Locoduino/CommandStation-EX-LaBox/Release_Notes/Railcom/La Box.jpg

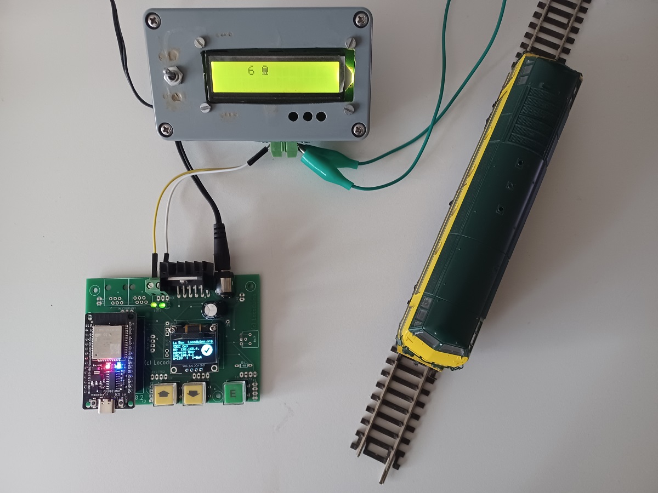
Release_Notes/Railcom/La Box.jpg
