Locoduino/CommandStation-EX-LaBox/Release_Notes/XpressNet/Double_RJ11E.jpg

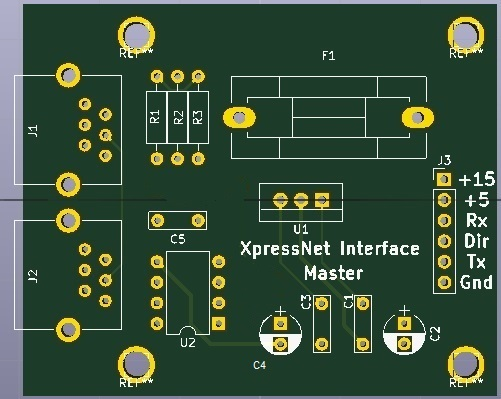
Release_Notes/XpressNet/Double_RJ11E.jpg
