Locoduino/CommandStation-EX-LaBox/Release_Notes/XpressNet/RJ11E.jpg

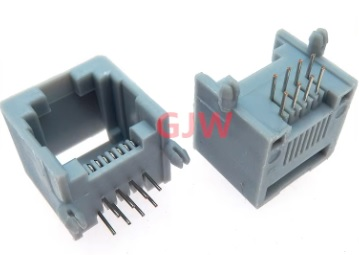
Release_Notes/XpressNet/RJ11E.jpg
