Locoduino/CommandStation-EX-LaBox/Release_Notes/XpressNet/Xpress1.jpg

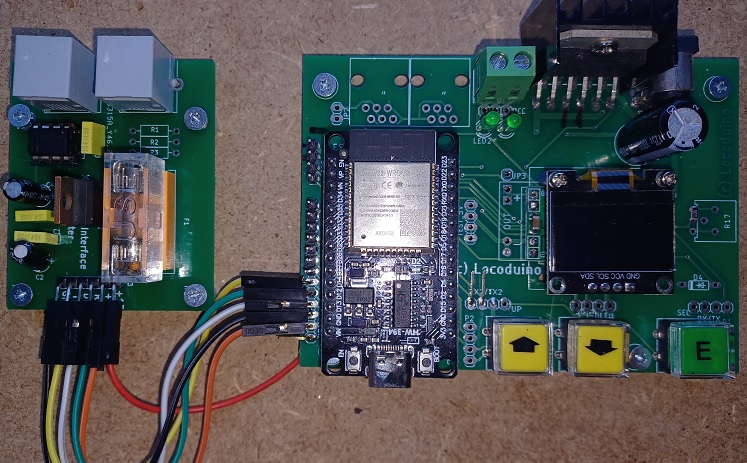
Release_Notes/XpressNet/Xpress1.jpg
