Locoduino/CommandStation-EX-LaBox/hmiConfig.h

/*
 * LaBox Project
 * Parameters
 * @Author : Cedric Bellec
 *	@Organization : Locoduino.org
 */

#ifndef HMICONFIG_H
#define HMICONFIG_H

// Pins
#define PIN_LEDBUILTIN           2
#define PIN_CURRENT_MES         36
#define PIN_VOLTAGE_MES         34

#ifdef USE_HMI
//---------------------- HMI section ------------------------------------
#define HMI_I2C_ADDR            0x3C
#define SCREEN_WIDTH            128         // OLED display width, in pixels
#define SCREEN_HEIGHT           64          // OLED display height, in pixels
#define HMI_Rotation            HMI_SCREEN_ROTATION           // 1 : 90°, 2 : 180°, 3 : 270°

// Pins
#define PIN_BTN_SEL             18
#define PIN_BTN_BTNUP           23
#define PIN_BTN_BTNDWN          19

// U/I correctors
#define HMI_VoltageK            0.0068      // Voltage scaling coefficient
#define HMI_CurrentK            0.9        	// Current scaling coefficient
#define HMI_deltaCurrent				HMI_CURRENTDELTA			// Current value shift with I=0
// Stack / string allocation sizes
#define HMI_StackNbCarElt       20          // 20 elements into the stack
#define HMI_EventMaxToDisplay   5           // We can display in full screnn 7 lines of event
#define HMI_MessageSize         20          // 20 characters for on message // Voir si il faut maintenir
#define HMI_MenueMessageSize    20          // 20 characters for un caption in menu
#define LineCarNbMax            20          // 1 ligne with FreeSerif9pt7b police, you can show 20 caracters max.
#define HMI_NbMemorisedTrain    10          // 
#define nbCycleToWaitWifi       50        
//--- Orders
#define HMI_OrderForward        20      
#define HMI_OrderBack           21
#define HMI_OrderStop           22 
#define HMI_OrderFunction       23
#define HMI_OrderStopAll        24  
#define HMI_StartDCC            25
#define HMI_ShortCurcuit        26
#define HMI_WifiWaiting         27
#define HMI_noWifi              28
#define HMI_WifiOk              29
//--- Display effects
#define HMI_LowEffect           500
#define HMI_FastEffect          100
#define HMI_DataRefesh          1000
#define HMI_DisplayRefesh       100
#define HMI_TimeOutMenu         30000     // in milliseconds
//--- HMITrain
#define HMITrain_NbMaxFunctions 28
#define HMITrain_NbStep         128
#define HMITrain_RectHeight     5
#define HMITrain_RectWidth      8
#define HMITrain_RectSpace      1
//--- Menu
#define HMI_Menu_OnLine         201
#define HMI_Menu_OffLine        202
#define HMI_Menu_WifiOn         203
#define HMI_Menu_WifiOff        204
#define NbMaxLineVisible        5

#define SPEED_VALUE_UNCHANGED		255

#define MENUNOTINIT             300
#define MENUEXIT                301
#define MENUCHANGETOCHILD       302
#define MENUCHOSEN              303
#define MENUTRAINADDRREAD       304
#define MENUTRAINCVREAD					305
#define MENUTRAINCVWRITE				306
#define MENUTRAINIDENT					307
#define MENUSHUTTLESAMPLE				308
#define MENUDCDCCMODE						309
#define MENUPHYSICALMES					310
#define MENUPROGMODE						311
#define MENUSETTINGS						312

#define MENUINFORMATION_ABOUT		400
#define MENUINFORMATION_WIFI		401
#define MENUINFORMATION_EXCOMM	402

#define MENUTYPECOMEBCK         0x8000
#define MENUTYPELIST            0x7999
#define MENUACTION              0x7998
#define MENUOPENSCREEN          0x7997
//#define MENUTYPEITEM            312


    // Message by language : French
// maximum line size : 					 ++++++++++++++++++++
#define TXT_Forward             "AV"
#define TXT_Back                "AR"
#define TXT_Forwardl            "Avance"
#define TXT_Backl               "Recule"
#define TXT_Stop                "Stop"
#define TXT_Function            "F"
#define TXT_StopAll             "<ARRET DCC>"
#define TXT_StartDCC            "<DCC On>"
#define TXT_ShortCircuit        "COURT-CIRCUIT"
#define TXT_MenuDCCOffLine      "Power ON/OFF"
#define TXT_MenuOnLine          "En ligne"
#define TXT_MenuOffLine         "Hors ligne"
#define TXT_MenuResetConfirm    "Confirmation Reset"
#define TXT_MenuYes             "Oui"
#define TXT_MenuNo              "Non"
#define TXT_MenuParams          "Parametres"
#define TXT_MenuInfos						"Informations"
#define TXT_MenuAbout						"A propos de..."
#define TXT_MenuAboutCSEX				"CS-EX %s <sortie>"
#define TXT_MenuInfoButtons			"             <sortie>"
#define TXT_MenuProgButtons			" ^ v         <sortie>"
#define TXT_MenuWifiInfo        "WiFi"
#define TXT_MenuEXCOMMInfo			"EXCOMM"
#define TXT_MenuSoftReset       "Redemarrage"
#define TXT_MenuBack            "< Retour >"
#define TXT_MenuAddrRead        "Lecture adr Train"
#define TXT_MenuAddrRetry				"Relire"
#define TXT_MenuAddrQuit				"Quitter"
#define TXT_MenuCVRead        	"Lecture CV"
#define TXT_MenuCVWrite        	"Ecriture CV"
#define TXT_MenuIdent	        	"Ident. decodeur"
#define TXT_MenuShuttle	       	"Va&Vient EXRail"
#define TXT_MenuSettings       	"Reglages"
#define TXT_DcDccMode		       	"DC/DCC"
#define TXT_PhysicalMes         "Mesures U et I"
#define TXT_ProgMode		        "Mode Programmation"
#define TXT_TrainView           "Type de vue trains"
#define TXT_V1Train             "1 train"
#define TXT_V2Trains            "2 trains"
#define TXT_V3Trains            "3 trains"
#define TXT_DONOTRESTART				"Redémarrer LaBox !"
#define TXT_ON									"ON"
#define TXT_OFF									"OFF"
#define TXT_CHANGE							"Changer"
// maximum line size : 					 ++++++++++++++++++++
#define TXT_LstEvent            "Liste evenements"
#define TXT_WifiWaiting         "Connexion WiFi..."
#define TXT_noWifi              " !! Pas de WiFi !!"
#define TXT_WifiApOk            "...Wifi AP ok..."
#define TXT_WifiSTAOk           "...Wifi STA ok..."
#define TXT_BoxAddr             "Adresse Box:"
#define TXT_WIFI								"WiFi"
#define TXT_RAILCOM							"Railcom"
// maximum line size : 					 ++++++++++++++++++++
#define TXT_CVREAD_LOGO					"LaBox     CV Lecture"
#define TXT_CVWRITE_LOGO				"LaBox    CV Ecriture"
#define TXT_CVRW_CVVALUE				"CV      Valeur"
#define TXT_CVRW_CVOK						"CV      Valeur OK"
#define TXT_CVRW_CVFAIL					"CV    Valeur ECHEC"
#define TXT_CVREAD_READING			"       Lecture..."
#define TXT_CVWRITE_WRITING			"      Ecriture..."
#define TXT_CVRW_OK							"AutreCV      Quitter"
#define TXT_CVRW_FAIL						"Refaire +/-  Quitter"
#define TXT_CVRW_READY					"+            Quitter"
#define TXT_CVREAD_ADDRESS			"+ -             Lire"
#define TXT_CVWRITE_ADDRESS			"+ -           Valeur"
#define TXT_CVWRITE_VALUE				"+ -           Ecrire"
// maximum line size : 					 ++++++++++++++++++++
#define TXT_IDENT_LOGO					"LaBox       Decodeur"
#define TXT_IDENT_READING7			"         Lecture cv7"
#define TXT_IDENT_READING8			"         Lecture cv8"
#define TXT_IDENT_LOCOADDRESS		"+ -           Lancer"
#define TXT_IDENT_ERRORCV7			"ERREUR CV7"
#define TXT_IDENT_ERRORCV8			"ERREUR CV8 cv7=%d"
#define TXT_IDENT_UNKNOWNID			"Inconnu cv8=%d"
#define TXT_IDENT_SEENMRA				"See NMRA 9.2.2.5 pdf"
#define TXT_IDENT_VERSION				"Version: %d/%d"
// maximum line size : 					 ++++++++++++++++++++
#define TXT_SHUTTLE_LOGO				"LaBox EXRail shuttle"
#define TXT_SHUTTLE_RUNNING			"Va&Vient EN ROUTE"
#define TXT_SHUTTLE_STOP				"Stop"
// maximum line size : 					 ++++++++++++++++++++
#define TXT_DCDCC_LOGO					"LaBox   DC/DCC mode"
#define TXT_DCDCC_DCRUNNING			"DC"
#define TXT_DCDCC_DCCRUNNING		"DCC"

    // Message by language : English
// maximum line size : 					 ++++++++++++++++++++
/*#define TXT_Forward             "FW"
#define TXT_Back                "BK"
#define TXT_Forwardl            "Forward"
#define TXT_Backl               "Back"
#define TXT_Stop                "Stop"
#define TXT_Function            "F"
#define TXT_StopAll             "!STOP ALL!"
#define TXT_StartDCC            "<DCC On>"
#define TXT_ShortCircuit        "SHORT-CIRCUIT"
#define TXT_MenuDCCOffLine      "Power ON/OFF"
#define TXT_MenuOnLine          "On line"
#define TXT_MenuOffLine         "Off line"
#define TXT_MenuDHCP            "DHCP"
#define TXT_MenuResetConfirm    "Reset confirmation ?"
#define TXT_MenuYes             "Yes"
#define TXT_MenuNo              "No"
#define TXT_MenuParams          "Parameters"
#define TXT_MenuInfos						"Informations"
#define TXT_MenuAbout						"About..."
#define TXT_MenuAboutCSEX				"CS-EX %s   <quit>"
#define TXT_MenuInfoButtons			"               <quit>"
#define TXT_MenuProgButtons			" ^ v           <quit>"
#define TXT_MenuWifiInfo        "WiFi"
#define TXT_MenuEXCOMMInfo			"EXCOMM"
#define TXT_MenuCAN             "Networks CAN"
#define TXT_MenuSoftReset       "Reboot"
#define TXT_MenuBack            "< Return >"
#define TXT_MenuAddrRead        "Read Train Addr"
#define TXT_MenuAddrRetry				"Retry"
#define TXT_MenuAddrQuit				"Quit"
#define TXT_MenuCVRead        	"Read CV"
#define TXT_MenuCVWrite        	"Write CV"
#define TXT_MenuIdent	        	"Identify decoder"
#define TXT_MenuShuttle	       	"Shuttle EXRail"
#define TXT_MenuSettings       	"Settings"
#define TXT_PhysicalMes         "Measures U and I"
#define TXT_ProgMode		        "Programming Mode"
#define TXT_TrainView           "Train view"
#define TXT_V1Train             "1 train"
#define TXT_V2Trains            "2 trains"
#define TXT_V3Trains            "3 trains"
#define TXT_DONOTRESTART				"Restart LaBox !"
#define TXT_ON									"ON"
#define TXT_OFF									"OFF"
#define TXT_CHANGE							"Change"
// maximum line size : 					 ++++++++++++++++++++
#define TXT_LstEvent            "Event list"
#define TXT_WifiWaiting         "Connection WiFi..."
#define TXT_noWifi              " !! No WiFi !!"
#define TXT_WifiApOk            "...Wifi AP ok..."
#define TXT_WifiSTAOk           "...Wifi STA ok..."
#define TXT_BoxAddr             "Box address :"
#define TXT_WIFI								"WiFi"
#define TXT_RAILCOM							"Railcom"
// maximum line size : 					 ++++++++++++++++++++
#define TXT_CVREAD_LOGO					"LaBox        CV Read"
#define TXT_CVWRITE_LOGO				"LaBox       CV Write"
#define TXT_CVRW_CVVALUE				"CV      Value"
#define TXT_CVRW_CVOK						"CV      Value OK"
#define TXT_CVRW_CVFAIL					"CV      Value FAIL"
#define TXT_CVREAD_READING			"       Reading..."
#define TXT_CVWRITE_WRITING			"       Writing..."
#define TXT_CVRW_OK							"OtherCV         Quit"
#define TXT_CVRW_FAIL						"Redo +/-        Quit"
#define TXT_CVRW_READY					"+               Quit"
#define TXT_CVREAD_ADDRESS			"+ -             Read"
#define TXT_CVWRITE_ADDRESS			"+ -            Value"
#define TXT_CVWRITE_VALUE				"+ -            Write"
// maximum line size : 					 ++++++++++++++++++++
#define TXT_IDENT_LOGO					"LaBox        Decoder"
#define TXT_IDENT_READING7			"         Reading cv7"
#define TXT_IDENT_READING8			"         Reading cv8"
#define TXT_IDENT_LOCOADDRESS		"+ -            Start"
#define TXT_IDENT_ERRORCV7			"ERROR CV7"
#define TXT_IDENT_ERRORCV8			"ERROR CV8 cv7=%d"
#define TXT_IDENT_UNKNOWNID			"Unknown cv8=%d"
#define TXT_IDENT_SEENMRA				"See NMRA 9.2.2.5 pdf"
#define TXT_IDENT_VERSION				"Version: %d/%d"
// maximum line size : 					 ++++++++++++++++++++
#define TXT_SHUTTLE_LOGO				"LaBox EXRail shuttle"
#define TXT_SHUTTLE_RUNNING			"Shuttle RUNNING"
#define TXT_SHUTTLE_STOP				"Stop"
// maximum line size : 					 ++++++++++++++++++++
#define TXT_DCDCC_LOGO					"LaBox   DC/DCC mode"
#define TXT_DCDCC_DCRUNNING			"DC"
#define TXT_DCDCC_DCCRUNNING		"DCC"
*/

//---------------------- Global section ---------------------------------
#define Labox_StateDCCOFF        101
#define Labox_StateDCCON         102
#define Labox_StateSHORTCIRCUIT  103

#endif
#endif
