Locoduino/CommandStation-EX-LaBox/Z21Throttle.cpp

/*
 *  © 2023 Thierry Paris / Locoduino
 *  © 2023,2024 Harald Barth
 *  All rights reserved.
 *  
 *  This file is part of CommandStation-EX-Labox
 *
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
 *  You should have received a copy of the GNU General Public License
 *  along with CommandStation.  If not, see <https://www.gnu.org/licenses/>.
 */
#include <Arduino.h>
#include "defines.h"

#ifdef ENABLE_Z21

#include "Z21Throttle.h"
#include "DCC.h"
#include "WifiESP32.h"
#include "DCCWaveform.h"
#include "StringFormatter.h"
#include "Turnouts.h"
#include "Sensors.h"
#include "DIAG.h"
#include "GITHUB_SHA.h"
#include "version.h"
#include "EXRAIL2.h"
#include "TrackManager.h"
#include "DCCTimer.h"
#include "LaboxModes.h"
#ifdef USE_HMI
	#include "hmi.h"
#endif

static std::vector<NetworkClientUDP> clientsUDP; // a list to hold all UDP clients

bool Z21Throttle::DIAGBASE=false;
bool Z21Throttle::DIAGRWCV=false;
bool Z21Throttle::DIAGBROADCAST=false;
bool Z21Throttle::DIAGDATA=false;
bool Z21Throttle::DIAGVERBOSE=false;

#define DIAG_Z21	 				if (Z21Throttle::DIAGBASE) DIAG
#define DIAG_Z21RWCV			if (Z21Throttle::DIAGRWCV) DIAG
#define DIAG_Z21BROADCAST	if (Z21Throttle::DIAGBROADCAST) DIAG
#define DIAG_Z21DATA		 	if (Z21Throttle::DIAGDATA) DIAG
#define DIAG_Z21VERBOSE	 	if (Z21Throttle::DIAGVERBOSE) DIAG

#define LOOPLOCOS(CAB)  for (int loco=0;loco<MAX_MY_LOCO;loco++)
#define LOOPTHROTTLES  Z21Throttle *pLoopThrottle = Z21Throttle::getFirstThrottle(); for (; pLoopThrottle != NULL; pLoopThrottle = pLoopThrottle->getNextThrottle())
#define LOOPCLIENTS  for (int clientId = 0; clientId < clientsUDP.size(); clientId++)

#define TURNOUT_FAR_TO_ADDRESS(inMSB, inLSB) ((inMSB << 8) + inLSB + 1)
#define TURNOUT_ADDRESS_TO_FARMSB(addr) ((byte)((addr-1) >> 8))
#define TURNOUT_ADDRESS_TO_FARLSB(addr) ((byte)((addr-1) & 0xFF))

Z21Throttle *Z21Throttle::firstThrottle=NULL;
byte Z21Throttle::commBuffer[100];
byte Z21Throttle::replyBuffer[20];

Z21Throttle* Z21Throttle::readWriteThrottle = NULL;
int Z21Throttle::cvAddress = -1;
int Z21Throttle::cvValue = -1;
int Z21EXCommItem::UDPport = Z21_UDPPORT;

void printClientsUDP();

WiFiUDP NetworkClientUDP::client;

bool Z21EXCommItem::begin() {
#ifdef DCCPP_DEBUG_MODE
	CircularBuffer::Test();
#endif
	bool retf = true;

	IPAddress ip;

	if (WiFi.getMode() == wifi_mode_t::WIFI_MODE_STA)
		ip = WiFi.localIP();
	if (WiFi.getMode() == wifi_mode_t::WIFI_MODE_AP)
		ip = WiFi.softAPIP();	

	uint8_t ret = NetworkClientUDP::client.begin(ip, UDPport);
	if (ret == 1) {
		retf = true;
		NetworkClientUDP::client.flush();
	}

	if (retf)
    DIAG(F("[Z21] UDP Connection started port %d. Z21 apps are available."), UDPport);
  else {
		DIAG(F("[Z21] UDP Connection failed. Z21 apps not available."));
		UDPport = -1;
	}

	return retf;
}

void Z21EXCommItem::getInfos(String *pMess1, String *pMess2, String *pMess3, byte maxSize) 
{
	char mess[maxSize*2];

	if (UDPport == -1)
		sprintf(mess, "[Z21] Not connected");
	else
		sprintf(mess, "[Z21] Port %d", UDPport);

	*pMess1 = mess;
}

void Z21EXCommItem::broadcastLoco(int16_t cab) {
	if (Z21Throttle::getFirstThrottle()!=NULL)		DIAG_Z21BROADCAST(F("[Z21] start Broadcasting loco %d ----"), cab);
	LOOPTHROTTLES {
		DIAG_Z21BROADCAST(F("[Z21] check throttle %d for loco %d %d %s"), pLoopThrottle->getClientId(), cab, pLoopThrottle->isBroadcastFlag() ? "BROADCAST" : "no broadcast");
		if (pLoopThrottle->isBroadcastFlag()) {
			int DB2 = cab & 0xFF;          // Extraction de inDB2
			int DB1 = (cab >> 8) & 0x3F;   // Extraction de inDB1
			pLoopThrottle->notifyLocoInfo(DB1, DB2);
		}
	}
	if (Z21Throttle::getFirstThrottle()!=NULL)		DIAG_Z21BROADCAST(F("[Z21] end Broadcasting locos   ----"));
}

void Z21EXCommItem::broadcastSensor(int16_t id, bool value) {
if (Z21Throttle::getFirstThrottle()!=NULL)			DIAG_Z21BROADCAST(F("[Z21] start Broadcasting sensors ----"));
	LOOPTHROTTLES {
		if (pLoopThrottle->isBroadcastFlag()) { // Should be broadcasted only with BROADCAST_LOCONET_DETECTOR flag...
			pLoopThrottle->notifySensor(id);
		}
	}
	if (Z21Throttle::getFirstThrottle()!=NULL)		DIAG_Z21BROADCAST(F("[Z21] end Broadcasting sensors   ----"));
}

void Z21EXCommItem::broadcastTurnout(int16_t id, bool isClosed) {
	if (Z21Throttle::getFirstThrottle()!=NULL)		DIAG_Z21BROADCAST(F("[Z21] start Broadcasting turnouts ----"));
	LOOPTHROTTLES {
		if (pLoopThrottle->isBroadcastFlag()) {
			int DB1 = TURNOUT_ADDRESS_TO_FARMSB(id);
			int DB2 = TURNOUT_ADDRESS_TO_FARLSB(id);
			pLoopThrottle->notifyTurnoutInfo((byte)DB1, (byte)DB2);
		}
	}
	if (Z21Throttle::getFirstThrottle()!=NULL)		DIAG_Z21BROADCAST(F("[Z21] end Broadcasting turnouts   ----"));
}

void Z21EXCommItem::broadcastPower() {
	if (Z21Throttle::getFirstThrottle()!=NULL)		DIAG_Z21BROADCAST(F("[Z21] start Broadcasting power ----"));
	LOOPTHROTTLES {
			pLoopThrottle->notifyTrPw(TrackManager::getMainPower() == POWERMODE::ON ? 1 : 0);
	}
	if (Z21Throttle::getFirstThrottle()!=NULL)		DIAG_Z21BROADCAST(F("[Z21] end Broadcasting power   ----"));
}

int readUdpPacket() {
	byte udp[UDPBYTE_SIZE];
	memset(udp, 0, UDPBYTE_SIZE);
	int len = NetworkClientUDP::client.read(udp, UDPBYTE_SIZE);
	if (len > 0) {
		for (int clientId = 0; clientId < clientsUDP.size(); clientId++) {
			if (clientsUDP[clientId].inUse) {
				if (clientsUDP[clientId].remoteIP == NetworkClientUDP::client.remoteIP() && clientsUDP[clientId].remotePort == NetworkClientUDP::client.remotePort()) {
					DIAG_Z21DATA(F("[Z21] %d: <- udp_len:%d"), clientId, len);

					// Black Z21 Android app send a bunch of 1000 bytes of value 0 ! 
					// Dont know why, but do not add this to the circular buffer !
					if (len < Z21_MAXIMAL_UDP_MSG_SIZE) {
						clientsUDP[clientId].pudpBuffer->PushBytes(udp, len);

						//if (Z21Throttle::Z21THROTTLEDATA) clientsUDP[clientId].pudpBuffer->printStatus();
					}
					else {
						DIAG_Z21(F("[Z21] %d: <- long message ignored : udp_len:%d   first byte : %d"), clientId, len, udp[0]);

						if (Z21Throttle::DIAGDATA) {
							for(int i = 0; i < 10; i++) {
								if (len > i*10) {
									DIAG_Z21DATA(F("   UDP %d-%d : 0x%02x 0x%02x 0x%02x 0x%02x 0x%02x 0x%02x 0x%02x 0x%02x 0x%02x 0x%02x"),
															i*10, (i*10)+9,
															(len > i*10)      ?udp[i*10]:0,
															(len > (i*10) + 1)?udp[(i*10)+1]:0,
															(len > (i*10) + 2)?udp[(i*10)+2]:0,
															(len > (i*10) + 3)?udp[(i*10)+3]:0,
															(len > (i*10) + 4)?udp[(i*10)+4]:0,
															(len > (i*10) + 5)?udp[(i*10)+5]:0,
															(len > (i*10) + 6)?udp[(i*10)+6]:0,
															(len > (i*10) + 7)?udp[(i*10)+7]:0,
															(len > (i*10) + 8)?udp[(i*10)+8]:0,
															(len > (i*10) + 9)?udp[(i*10)+9]:0);
								}
							}
						}
					}

					return clientId;
				}
			}
		}
	}

	return -1;
}

void Z21Throttle::loop() {
  if (Z21EXCommItem::UDPport < 0) {
		return;
	}

	int clientId = 0;

	// loop over all clients and remove inactive
	for (clientId = 0; clientId < clientsUDP.size(); clientId++) {
		if (!clientsUDP[clientId].inUse) {
			continue;
		}

		Z21Throttle* pThrottle = getOrAddThrottle(clientId); 

		if (pThrottle->lastHeartBeatDate != 0 && millis() - pThrottle->lastHeartBeatDate > Z21_TIMEOUT) {
			clientsUDP[clientId].connected = false;
		}

		// check if client is there and alive
		if (clientsUDP[clientId].inUse && !clientsUDP[clientId].connected) {
			DIAG(F("[Z21] Remove disconnected UDP client %d"), clientId);
			clientsUDP[clientId].inUse = false;
			printClientsUDP();
		}
	}

	int len = NetworkClientUDP::client.parsePacket();
	if (len > 0) {
		// Check if this IP is already in the client list.
		int clientId = 0;
		for (; clientId < clientsUDP.size(); clientId++) {
			if (clientsUDP[clientId].inUse) {
				if (clientsUDP[clientId].remoteIP == NetworkClientUDP::client.remoteIP() && clientsUDP[clientId].remotePort == NetworkClientUDP::client.remotePort()) {
					//DIAG_Z21VERBOSE(F("UDP client %d : %s Already connected"), clientId, clientsUDP[clientId].remoteIP.toString().c_str());
					break;
				}
			}
		}

		// If this IP is not already present, try tyo find the first slot available

		if (clientId >= clientsUDP.size()) {
			for (clientId = 0; clientId < clientsUDP.size(); clientId++) {
				if (!clientsUDP[clientId].inUse) {
					break;
				}
			}

			// If no empty slot found, add a new one.
			if (clientId >= clientsUDP.size()) {
				NetworkClientUDP nc;
				clientsUDP.push_back(nc);
			}

			clientsUDP[clientId].remoteIP = NetworkClientUDP::client.remoteIP();
			clientsUDP[clientId].remotePort = NetworkClientUDP::client.remotePort();
			clientsUDP[clientId].connected = true;
			clientsUDP[clientId].inUse = true;

			DIAG(F("[Z21] New UDP client %d, %s"), clientId, clientsUDP[clientId].remoteIP.toString().c_str());
			printClientsUDP();
			#ifdef USE_HMI
			if (hmi::CurrentInterface != NULL) hmi::CurrentInterface->NewClient(clientId, clientsUDP[clientId].remoteIP, 0);
			#endif
			// Fleischmann/Roco Android app starts with Power on !
			TrackManager::setMainPower(POWERMODE::ON);
			Z21Throttle* pThrottle = getOrAddThrottle(clientId); 
			if (pThrottle != NULL) {
		  	pThrottle->lastHeartBeatDate = millis();
//      	pThrottle->notifyTrPw(clientId, 1);
			}
		}

		clientId = readUdpPacket();

		if (clientId >= 0) {
			if (clientsUDP[clientId].ok()) {        
				Z21Throttle* pThrottle = getOrAddThrottle(clientId); 
			  pThrottle->lastHeartBeatDate = millis();

				if (pThrottle != NULL) {
					while(clientsUDP[clientId].pudpBuffer->GetCount() > 2)
						pThrottle->parse();
				}
			}
		}
	}
}

/** Print the list of assigned locomotives. */
void Z21Throttle::printLocomotives(bool addTab) {
	if (!Z21Throttle::DIAGBASE)
		return;

	DIAG(F("[Z21]       Locomotives ------------------"));
	for (int loco = 0; loco < MAX_MY_LOCO; loco++)
		if (this->cabs[loco] != 0)
			DIAG(F("[Z21] %s         %d : cab %d on throttle %c"), addTab ? "   ":"", loco, this->cabs[loco], this->clientid);
}

/** Print the list of UDP clients. */
void printClientsUDP() {
	if (!Z21Throttle::DIAGBASE) return;

	DIAG(F("[Z21]       UDP Clients ------------------"));
	for (int clientId = 0; clientId < clientsUDP.size(); clientId++)
		if (clientsUDP[clientId].ok())
			DIAG(F("[Z21]          %d %s: %s:%d"), clientId, clientsUDP[clientId].connected?"Connected":"Not connected", clientsUDP[clientId].remoteIP.toString().c_str(), clientsUDP[clientId].remotePort);
		else
			DIAG(F("[Z21]          %d unused"), clientId);
}

/** Print the list of throttles. */
void Z21Throttle::printThrottles(bool inPrintLocomotives) {
	if (!Z21Throttle::DIAGBASE)	return;

	DIAG(F("[Z21]       Throttles ---------------"));
	for (Z21Throttle* wt = firstThrottle; wt != NULL; wt = wt->nextThrottle) {
		if (wt->clientid == -1)
			DIAG(F("[Z21]          unused"));
		else {
			DIAG(F("[Z21]          %d : %d.%d.%d.%d:%d"), wt->clientid, 
			clientsUDP[wt->clientid].remoteIP[0], 
			clientsUDP[wt->clientid].remoteIP[1], 
			clientsUDP[wt->clientid].remoteIP[2], 
			clientsUDP[wt->clientid].remoteIP[3], 
			clientsUDP[wt->clientid].remotePort);

			if (inPrintLocomotives)
				wt->printLocomotives(true);
		}
	}
}

Z21Throttle* Z21Throttle::getOrAddThrottle(int clientId) {
	for (Z21Throttle* wt = firstThrottle; wt != NULL ; wt = wt->nextThrottle)  {
		if (wt->clientid == clientId)
			return wt; 
	}

	Z21Throttle *p = new Z21Throttle(clientId);
	printThrottles(false);
	return p;
}

/*void Z21Throttle::broadcastNotifyTurnout(uint16_t addr, bool isClosed) {
  for (Z21Throttle* wt = firstThrottle; wt != NULL ; wt = wt->nextThrottle)  {
    wt->notifyTurnoutInfo(addr, isClosed);
  }
}
void Z21Throttle::broadcastNotifySensor(uint16_t addr, bool state) {
  for (Z21Throttle* wt = firstThrottle; wt != NULL ; wt = wt->nextThrottle)  {
    wt->notifySensor(addr, state);
  }
}*/

void Z21Throttle::forget( byte clientId) {
	for (Z21Throttle* wt=firstThrottle; wt!=NULL ; wt=wt->nextThrottle)  
    	if (wt->clientid==clientId) {
			delete wt;
			break; 
		}
}

bool Z21Throttle::isThrottleInUse(int cab) {
	for (Z21Throttle* wt=firstThrottle; wt!=NULL ; wt=wt->nextThrottle)  
		if (wt->isCabInUse(cab)) return true;

	return false;
}

// One instance of Z21Throttle per connected client, so we know what the locos are 
 
Z21Throttle::Z21Throttle(int inClientId) {
	this->clientid = inClientId;
	DIAG_Z21(F("[Z21] new Throttle for client UDP %d"),this->clientid);
	this->nextThrottle = firstThrottle;
	this->firstThrottle = this;
	this->turnoutListHash = -1;  // make sure turnout list is sent once
	this->exRailSent = false;
	this->lastHeartBeatDate = 0;
	// Because if the LaBox restarts but not the Z21 app, the Z21 app will not resend the LAN_SET_BROADCASTFLAGS, we need to set the default value of broadcast flags to be able to broadcast loco and turnout infos to the app.
	this->broadcastFlags = BROADCAST_BASE; // by default, basic broadcast flag is on
	for (int loco=0;loco<MAX_MY_LOCO; loco++)
		this->cabs[loco]=0;
}

Z21Throttle::~Z21Throttle() {
	DIAG_Z21(F("[Z21] Deleting Throttle client UDP %d"),this->clientid);
	if (firstThrottle== this) {
		firstThrottle=this->nextThrottle;
		return;
	}

	for (Z21Throttle* wt=firstThrottle; wt!=NULL ; wt=wt->nextThrottle) {
		if (wt->nextThrottle==this) {
			wt->nextThrottle=this->nextThrottle;
			return;  
		}
	}
}

void Z21Throttle::write(byte* inpData, int inLengthData) {
	size_t size = 0;

//	if (this->dontReply)
//		return;
	
	int errorCode = NetworkClientUDP::client.beginPacket(clientsUDP[this->clientid].remoteIP, clientsUDP[this->clientid].remotePort);
	if (errorCode != 1) {
		DIAG_Z21(F("[Z21] %d: UDP beginPacket failed with error code %d"), this->clientid, errorCode);
		return;
	}
	size = NetworkClientUDP::client.write(inpData, inLengthData);
	errorCode = NetworkClientUDP::client.endPacket();
	if (errorCode != 1) {
		DIAG_Z21(F("[Z21] %d: UDP endPacket failed with error code %d"), this->clientid, errorCode);
		return;
	}
	
	DIAG_Z21DATA(F("[Z21] %d: %s SENT 0x%02x 0x%02x 0x%02x 0x%02x 0x%02x 0x%02x 0x%02x 0x%02x 0x%02x 0x%02x"), this->clientid,
                          size == 0 ? "BINARY NOT" :"",
                          (inLengthData > 0)?inpData[0]:0,
                          (inLengthData > 1)?inpData[1]:0,
                          (inLengthData > 2)?inpData[2]:0,
                          (inLengthData > 3)?inpData[3]:0,
                          (inLengthData > 4)?inpData[4]:0,
                          (inLengthData > 5)?inpData[5]:0,
                          (inLengthData > 6)?inpData[6]:0,
                          (inLengthData > 7)?inpData[7]:0,
                          (inLengthData > 8)?inpData[8]:0,
                          (inLengthData > 9)?inpData[9]:0);
}

// sizes : [       2        ][       2        ][inLengthData]
// bytes : [length1, length2][Header1, Header2][Data........]
bool Z21Throttle::notify(unsigned int inHeader, byte* inpData, unsigned int inLengthData, bool inXorInData) {
	int realLength = (inLengthData + 4 + (inXorInData == false ? 1 : 0));

	Z21Throttle::commBuffer[0] = realLength % 256;
	Z21Throttle::commBuffer[1] = realLength / 256;
	Z21Throttle::commBuffer[2] = inHeader % 256;
	Z21Throttle::commBuffer[3] = inHeader / 256;
	memcpy(Z21Throttle::commBuffer + 4, inpData, inLengthData);

	if (!inXorInData) {    // if xor byte not included in data, compute and write it !
		byte xxor = 0;

		for (unsigned int i = 0; i < inLengthData; i++)
			xxor ^= inpData[i];

		Z21Throttle::commBuffer[inLengthData+4] = xxor;
	}

	write(Z21Throttle::commBuffer, realLength);

	return true;
}

// sizes : [       2        ][       2        ][   1   ][inLengthData]
// bytes : [length1, length2][Header1, Header2][XHeader][Data........]
bool Z21Throttle::notify(unsigned int inHeader, unsigned int inXHeader, byte* inpData, unsigned int inLengthData, bool inXorInData) {
	int realLength = (inLengthData + 5 + (inXorInData == false ? 1 : 0));

	Z21Throttle::commBuffer[0] = realLength % 256;
	Z21Throttle::commBuffer[1] = realLength / 256;
	Z21Throttle::commBuffer[2] = inHeader % 256;
	Z21Throttle::commBuffer[3] = inHeader / 256;
	Z21Throttle::commBuffer[4] = inXHeader;
	memcpy(Z21Throttle::commBuffer + 5, inpData, inLengthData);

	if (!inXorInData) {    // if xor byte not included in data, compute and write it !
		byte xxor = inXHeader;

		for (unsigned int i = 0; i < inLengthData; i++)
			xxor ^= inpData[i];

		Z21Throttle::commBuffer[inLengthData + 5] = xxor;
	}

	write(Z21Throttle::commBuffer, realLength);

	return true;
}

// sizes : [       2        ][       2        ][   1   ][ 1 ][inLengthData]
// bytes : [length1, length2][Header1, Header2][XHeader][DB0][Data........]
bool Z21Throttle::notify(unsigned int inHeader, unsigned int inXHeader, byte inDB0, byte* inpData, unsigned int inLengthData, bool inXorInData) {
	int realLength = (inLengthData + 6 + (inXorInData == false ? 1 : 0));

	Z21Throttle::commBuffer[0] = realLength % 256;
	Z21Throttle::commBuffer[1] = realLength / 256;
	Z21Throttle::commBuffer[2] = inHeader % 256;
	Z21Throttle::commBuffer[3] = inHeader / 256;
	Z21Throttle::commBuffer[4] = inXHeader;
	Z21Throttle::commBuffer[5] = inDB0;
	memcpy(Z21Throttle::commBuffer + 6, inpData, inLengthData);

	if (!inXorInData) {   // if xor byte not included in data, compute and write it !
		byte xxor = inXHeader^inDB0;

		for (unsigned int i = 0; i < inLengthData; i++)
			xxor ^= inpData[i];

		Z21Throttle::commBuffer[inLengthData + 6] = xxor;
	}

	write(Z21Throttle::commBuffer, realLength);

	return true;
}

void Z21Throttle::notifyStatus() {
	Z21Throttle::replyBuffer[0] = 0; // main current 1
	Z21Throttle::replyBuffer[1] = 0; // main current 2
	Z21Throttle::replyBuffer[2] = 0; // prog current 1
	Z21Throttle::replyBuffer[3] = 0; // prog current 2
	Z21Throttle::replyBuffer[4] = 0; // filtered main current 1
	Z21Throttle::replyBuffer[5] = 0; // filtered main current 2
	Z21Throttle::replyBuffer[6] = 0; // Temperature 1
	Z21Throttle::replyBuffer[7] = 0; // Temperature 2
	Z21Throttle::replyBuffer[8] = 5; // Supply voltage 1
	Z21Throttle::replyBuffer[9] = 0; // supply voltage 2
	Z21Throttle::replyBuffer[10] = 16; // VCC voltage 1 
	Z21Throttle::replyBuffer[11] = 0; // VCC voltage 2
	Z21Throttle::replyBuffer[12] = 0b00000000;	// CentralState 
	Z21Throttle::replyBuffer[13] = 0b00000000; // CentralStateEx
	Z21Throttle::replyBuffer[14] = 0;
	Z21Throttle::replyBuffer[15] = 0;
	notify(HEADER_LAN_SYSTEMSTATE, Z21Throttle::replyBuffer, 16, true);
}

int Z21Throttle::getOrAddLoco(int cab) {
	int loco = 0;

	// try to find the cab
	for (; loco < MAX_MY_LOCO; loco++) {
		if (this->cabs[loco] == cab) 
			return loco;
	}

	int foundLoco = -1;

	// not found ! Add the cab.
	for (loco = 0; loco < MAX_MY_LOCO; loco++) {
		if (this->cabs[loco] == 0) {
			this->cabs[loco] = cab;
			foundLoco = loco;
			break;
		}
	}

	// if no place available...
	if (foundLoco == -1) {
		printLocomotives();
		return -1;
	}

	return loco;
}

int Z21Throttle::countLocos() {
	int count = 0;

	for (int loco = 0; loco < MAX_MY_LOCO; loco++) {
		if (this->cabs[loco] != 0)
			count++;
	}

	return count;
}

bool Z21Throttle::isCabInUse(int cab) { 
	// try to find the cab
	for (int loco = 0; loco < MAX_MY_LOCO; loco++) {
		if (this->cabs[loco] == cab) 
			return true;
	}

	return false;
}

void Z21Throttle::notifyLocoInfo(byte inMSB, byte inLSB) {
	int locoAddress = ((inMSB & 0x3F) << 8) + inLSB;
	int loco = getOrAddLoco(locoAddress);

	if (loco == -1)
	    return; //'Too many locos !'

  LocoSlot *slot = LocoSlot::getSlot(locoAddress, true);
	if (slot == NULL) {
		DIAG_Z21(F("[Z21] %d: Loco %d not found"), this->clientid, locoAddress);
		return;
	}

	Z21Throttle::replyBuffer[0] = inMSB;	// loco address msb
	Z21Throttle::replyBuffer[1] = inLSB; // loco address lsb
	Z21Throttle::replyBuffer[2] = B00000100; // 0000CKKK	 C = already controlled    KKK = speed steps 000:14, 010:28, 100:128
	Z21Throttle::replyBuffer[3] = slot->getTargetSpeed() & 0x7F; // RVVVVVVV  R = forward    VVVVVVV = speed
	if ((slot->getTargetSpeed() & 0x80) !=0) bitSet(Z21Throttle::replyBuffer[3], 7);

	uint32_t functionMap = slot->getFunctions();

	// Byte 4: 0DSLFGHJ
	// D = double traction  S = Smartsearch  L = F0  F = F4  G = F3  H = F2  J = F1
	Z21Throttle::replyBuffer[4] = (functionMap >> 1) & 0xF; // function F1 to F5
	if (functionMap & 1) // set F0 (Light)
		Z21Throttle::replyBuffer[4] += 16;
	functionMap >>=5; // shift out the 5 bits which are not needed any more

	Z21Throttle::replyBuffer[5] = functionMap & 0xFF; // function  F5 to F12;  F5 is bit0
	functionMap >>=8; // shift out 8 more
	Z21Throttle::replyBuffer[6] = functionMap & 0xFF; // function F13 to F20; F13 is bit0
	functionMap >>=8; // shift out 8 more
	Z21Throttle::replyBuffer[7] = functionMap & 0xFF; // function F21 to F28; F21 is bit0
	functionMap >>=8; // shift out 8 more
	Z21Throttle::replyBuffer[8] = functionMap & 0xFF; // function F29 to F31; F28 is bit0
	
	notify(HEADER_LAN_XPRESS_NET, LAN_X_HEADER_LOCO_INFO, Z21Throttle::replyBuffer, 9, false);
	
	DIAG_Z21BROADCAST(F("[Z21] %d: Notify loco %d"), this->clientid, locoAddress);

  if (TrackManager::getMainPower()==POWERMODE::OFF) 
    notifyTrPw(0);
  else 
    notifyTrPw(1);
}

// This variant is called from the broadcast function when turnouts change
// from the "inside" where we know the turnout state
void Z21Throttle::notifyTurnoutInfo(uint16_t addr, bool isClosed) {
  notifyTurnoutInfo(TURNOUT_ADDRESS_TO_FARMSB(addr), TURNOUT_ADDRESS_TO_FARLSB(addr), isClosed);
}

// This variant is called from the Xnet protocol when the client queries
// the state of a turnout (which may or may not exist)
void Z21Throttle::notifyTurnoutInfo(byte inMSB, byte inLSB) {
  uint16_t addr = TURNOUT_FAR_TO_ADDRESS(inMSB, inLSB);
  Turnout *tt = Turnout::get(addr);
  if (tt) {
    notifyTurnoutInfo(inMSB, inLSB, tt->isClosed());
    return;
  }
  // if the tt does not exist we fall through with replyBuffer set to invalid
	Z21Throttle::replyBuffer[0] = inMSB;	// turnout address msb
	Z21Throttle::replyBuffer[1] = inLSB; // turnout address lsb
  Z21Throttle::replyBuffer[2] = B00000011; //  000000ZZ  ZZ: 00=not-switched 01=pos1 10=pos2 11=invalid
  DIAG_Z21BROADCAST(F("[Z21] Throttle %d : Turnoutinfo %d (invalid)"), clientid, addr);
  notify(HEADER_LAN_XPRESS_NET, LAN_X_HEADER_TURNOUT_INFO, Z21Throttle::replyBuffer, 3, false);
}

// This variant is called when we know that turnout exists and it's state.
void Z21Throttle::notifyTurnoutInfo(byte inMSB, byte inLSB, bool isClosed) {
  Z21Throttle::replyBuffer[0] = inMSB;
  Z21Throttle::replyBuffer[1] = inLSB;
  char c;
  if (isClosed) {
    Z21Throttle::replyBuffer[2] = B00000010; // 000000ZZ  ZZ: 00=not-switched 01=pos1 10=pos2 11=invalid
    c = 'c';
  } else {
    Z21Throttle::replyBuffer[2] = B00000001;
    c = 't';
  }
  uint16_t addr = TURNOUT_FAR_TO_ADDRESS(inMSB, inLSB);
  DIAG_Z21BROADCAST(F("[Z21] Throttle %d : Turnoutinfo %d %c"), clientid, addr, c);
  notify(HEADER_LAN_XPRESS_NET, LAN_X_HEADER_TURNOUT_INFO, Z21Throttle::replyBuffer, 3, false);
}

void Z21Throttle::notifySensor(uint16_t addr) {
  Sensor *s = Sensor::get(addr);
  if (s) {
    notifySensor(addr, s->active);
  }
}

void Z21Throttle::notifySensor(uint16_t addr, bool state) {
  Z21Throttle::replyBuffer[0] = 0x01; // Status in first info byte
  Z21Throttle::replyBuffer[1] = (byte)(addr & 0xFF);
  Z21Throttle::replyBuffer[2] = (byte)(addr >> 8);
  Z21Throttle::replyBuffer[3] = state;
  DIAG_Z21BROADCAST(F("[Z21] Throttle %d : notifySensor %d 0x%x"), clientid, addr, Z21Throttle::replyBuffer[3]);
  notify(HEADER_LAN_LOCONET_DETECTOR, Z21Throttle::replyBuffer, 4, false);
}

void Z21Throttle::notifyLocoMode(byte inMSB, byte inLSB) {
	Z21Throttle::replyBuffer[0] = inMSB;	// loco address msb
	Z21Throttle::replyBuffer[1] = inLSB; // loco address lsb
	Z21Throttle::replyBuffer[2] = B00000000; // 00000000	DCC   00000001 MM
	notify(HEADER_LAN_GET_LOCOMODE, Z21Throttle::replyBuffer, 3, true);
}

void Z21Throttle::notifyTrPw(byte TrPw) {
  Z21Throttle::replyBuffer[0] = 0x22; 
  Z21Throttle::replyBuffer[1] = 0x2-(TrPw*2) ; // power off or on
  notify(HEADER_LAN_XPRESS_NET, LAN_X_STATUS_CHANGED, Z21Throttle::replyBuffer, 2, false);

	DIAG_Z21BROADCAST(F("[Z21] %d: Notify power %d "), this->clientid, TrPw);
}

void Z21Throttle::notifyFirmwareVersion() {
	Z21Throttle::replyBuffer[0] = 0x01;	// Version major in BCD
	Z21Throttle::replyBuffer[1] = 0x23;	// Version minor in BCD
	notify(HEADER_LAN_XPRESS_NET, LAN_X_HEADER_FIRMWARE_VERSION, 0x0A, Z21Throttle::replyBuffer, 2, false);
}

void Z21Throttle::notifySerialNumber() {
	Z21Throttle::replyBuffer[0] = 0x02;	// Serial number little endian
	Z21Throttle::replyBuffer[1] = 0x05;	// 
	notify(HEADER_LAN_GET_SERIAL_NUMBER, Z21Throttle::replyBuffer, 2, false);
}

void Z21Throttle::notifyHWInfo() {
	Z21Throttle::replyBuffer[0] = 0x00;	// Hardware type in BCD on int32
	Z21Throttle::replyBuffer[1] = 0x02;	// Hardware type in BCD on int32
	Z21Throttle::replyBuffer[2] = 0x00;	// Hardware type in BCD on int32
	Z21Throttle::replyBuffer[3] = 0x00;	// Hardware type in BCD on int32
	Z21Throttle::replyBuffer[4] = 0x23;	// Firmware version in BCD on int32
	Z21Throttle::replyBuffer[5] = 0x01;	// Firmware version in BCD on int32
	Z21Throttle::replyBuffer[6] = 0x00;	// Firmware version in BCD on int32
	Z21Throttle::replyBuffer[7] = 0x00;	// Firmware version in BCD on int32
	notify(HEADER_LAN_GET_HWINFO, Z21Throttle::replyBuffer, 8, true);
}

void Z21Throttle::notifyCvNACK(int inCvAddress) {
	Z21Throttle::replyBuffer[0] = highByte(inCvAddress); // cv address msb
	Z21Throttle::replyBuffer[1] = lowByte(inCvAddress); // cv address lsb
	notify(HEADER_LAN_XPRESS_NET, LAN_X_HEADER_CV_NACK, LAN_X_DB0_CV_NACK, Z21Throttle::replyBuffer, 0, false);
}

void Z21Throttle::notifyCvRead(int inCvAddress, int inValue) {
	Z21Throttle::replyBuffer[0] = highByte(inCvAddress); // cv address msb
	Z21Throttle::replyBuffer[1] = lowByte(inCvAddress); // cv address lsb
	Z21Throttle::replyBuffer[2] = inValue; // cv value
	notify(HEADER_LAN_XPRESS_NET, LAN_X_HEADER_CV_RESULT, 0x14, Z21Throttle::replyBuffer, 3, false);
}

void Z21Throttle::setSpeed(byte inNbSteps, byte inDB1, byte inDB2, byte inDB3) {
	bool isForward = bitRead(inDB3, 7);
	byte speed = inDB3;
	bitClear(speed, 7);

	DIAG_Z21(F("[Z21] %d: speed %d"), clientid, speed * (isForward ? 1:-1));

	int locoAddress = ((inDB1 & 0x3F) << 8) + inDB2;

	if (getOrAddLoco(locoAddress) == -1) {
		DIAG_Z21(F("[Z21] %d: loco %d cannot be added"), clientid, locoAddress);
		return;
	}

	DCC::setThrottle(locoAddress, speed, isForward);
}

void Z21Throttle::setTurnout(byte addrMSB, byte addrLSB, byte command) {
  // 10Q0A00P
  // A=0 ... Deactivate turnout output
  // A=1 ... Activate turnout output
  // P=0 ... Select output 1 of the turnout
  // P=1 ... Select output 2 of the turnout
  // Q=0 ... Execute command immediately
  //         means that the client (app/mouse) does send activate and deactive
  // Q=1 ... From Z21 FW V1.24: Insert turnout command into the queue of Z21
  bool queue = (command & B00100000) != 0;
  bool activate = (command & B00001000) != 0;
  byte output = command & B00000001;

  uint16_t addr = TURNOUT_FAR_TO_ADDRESS(addrMSB, addrLSB);
  DIAG_Z21(F("[Z21] Throttle %d : turnout %d cmd 0x%x"), clientid, addr, command);

	if (!Turnout::exists(addr)) {
		if (addr == 0) {
			DIAG(F("[Z21] Turnout address 0 is invalid"));
			return;
		}
		
		// If turnout does not exist, create it
		int mainaddr = ((addr - 1) / 4) + 1;
		int subaddr = (addr - 1) % 4;
		DCCTurnout::create(addr, mainaddr, subaddr);
	  DIAG_Z21(F("[Z21] Throttle %d : turnout %d created"), clientid, addr);
	}

  (void)queue; // We probably do not need to care (as we are a CS that maps to internal
               // turnouts and not to accessory commands) about the difference.
  if (activate) {
    Turnout::setClosed(addr, output == 1);
  } // else ignore the deactivate message
  //notifyTurnoutInfo(addrMSB, addrLSB); // sent for both activate and deactivate
}

//
// TODO Pass through a text message to avoid multi thread locks...
//

void Z21Throttle::setFunction(byte inDB1, byte inDB2, byte inDB3) {
	// inDB3 :  TTNN NNNN		TT:00 off, TT:01 on; TT:10 toggle   NNNNNN function number

	byte action = bitRead(inDB3, 6) + 2 * bitRead(inDB3, 7);
	byte function = inDB3;
	bitClear(function, 6);
	bitClear(function, 7);
	bool activeFlag = action == 0b01;

	DIAG_Z21(F("[Z21] %d: function %d %s"), clientid, function, activeFlag?"ON":"OFF");

	int locoAddress = ((inDB1 & 0x3F) << 8) + inDB2;
	if (getOrAddLoco(locoAddress) == -1) {
		DIAG_Z21(F("[Z21] %d: loco %d cannot be added"), clientid, locoAddress);
		return;
	}

	if (action == 0b10)	{	// toggle
		bool isActivated = DCC::getFn(locoAddress, function);
		activeFlag = !isActivated;
	}

	DCC::setFn(locoAddress, function, activeFlag);
	/*if ((this->broadcastFlags & BROADCAST_BASE) != 0)
		notifyLocoInfo(inDB1, inDB2);*/
}

//
// TODO Pass through a text message to avoid multi thread locks...
//

void Z21CvValueCallback(int16_t inValue)
{
	Z21Throttle::cvValue = inValue;

	if (inValue == -1)
	{
		Z21Throttle::readWriteThrottle->notifyCvNACK(Z21Throttle::cvAddress);
	}
	else
	{
		Z21Throttle::readWriteThrottle->notifyCvRead(Z21Throttle::cvAddress, inValue);
	}

	Z21Throttle::readWriteThrottle = NULL;
}

void Z21Throttle::cvReadProg(byte inDB1, byte inDB2) {
	if (Z21Throttle::readWriteThrottle != NULL)
		return;

	int cvAddress = ((inDB1 & 0x3F) << 8) + inDB2 + 1;

	DIAG_Z21RWCV(F("[Z21] %d: cvRead Prog %d"), clientid, cvAddress);

	Z21Throttle::readWriteThrottle = this;
	Z21Throttle::cvAddress = cvAddress - 1;

	void (*ptr)(int16_t) = &Z21CvValueCallback;
	DCC::readCV(cvAddress, ptr);
}

// Working as cvReadProg for the moment...
void Z21Throttle::cvReadMain(byte inDB1, byte inDB2) {
/*	if (Z21Throttle::readWriteThrottle != NULL)
		return;

	int cvAddress = ((inDB1 & 0x3F) << 8) + inDB2 + 1;

	DIAG_Z21RWCV(F("[Z21] %d: cvRead Main cv %d"), clientid, cvAddress);

	Z21Throttle::readWriteThrottle = this;
	Z21Throttle::cvAddress = cvAddress - 1;

	void (*ptr)(int16_t) = &Z21CvValueCallback;
	DCC::readCV(cvAddress, ptr);*/
}

//
// TODO Pass through a text message to avoid multi thread locks...
//

void Z21Throttle::cvWriteProg(byte inDB1, byte inDB2, byte inDB3) {
	if (Z21Throttle::readWriteThrottle != NULL)
		return;

	int cvAddress = ((inDB1 & 0x3F) << 8) + inDB2 + 1;

	DIAG_Z21RWCV(F("[Z21] %d: cvWrite Prog cv %d value %d"), clientid, cvAddress, inDB3);

	Z21Throttle::readWriteThrottle = this;
	Z21Throttle::cvAddress = cvAddress - 1;

	void (*ptr)(int16_t) = &Z21CvValueCallback;
	DCC::writeCVByte(cvAddress, inDB3, ptr);
}

// Working as cvReadProg for the moment...
int Z21Throttle::cvReadPom(byte inDB1, byte inDB2, byte inDB3, byte inDB4) {
	int cvAddress = ((inDB3 & B00000011) << 8) + inDB4 + 1;
/*	int locoAddress = ((inDB1 & 0x3F) << 8) + inDB2;

	DIAG_Z21RWCV(F("[Z21] %d: cvRead Pom Loco %d cv %d"), clientid, locoAddress, cvAddress);

	Z21Throttle::cvAddress = cvAddress - 1;

	void (*ptr)(int16_t) = &Z21CvValueCallback;
	DCC::readCV(cvAddress, ptr);*/
	return cvAddress;
}

void Z21Throttle::cvWriteBytePom(byte inDB1, byte inDB2, byte inDB3, byte inDB4, byte inDB5) {
	int locoAddress = ((inDB1 & 0x3F) << 8) + inDB2;
	int cvAddress = ((inDB3 & B00000011) << 8) + inDB4 + 1;

	DIAG_Z21RWCV(F("[Z21] %d: cvWrite Byte Pom Loco %d cv %d = %d"), clientid, locoAddress, cvAddress, inDB5);

	Z21Throttle::cvAddress = cvAddress - 1;

	DCC::writeCVByteMain(locoAddress, cvAddress, inDB5);
}

void Z21Throttle::cvWriteBitPom(byte inDB1, byte inDB2, byte inDB3, byte inDB4, byte inDB5) {
	int locoAddress = ((inDB1 & 0x3F) << 8) + inDB2;
	int cvAddress = ((inDB3 & B00000011) << 8) + inDB4 + 1;

	Z21Throttle::cvAddress = cvAddress - 1;

	byte bitNum = inDB5 & B00000011 << 8;
	bool value = inDB5 & B00000100;

	DIAG_Z21RWCV(F("[Z21] %d: cvWrite Bit Pom Loco %d cv %d : bit %d = %s"), clientid, locoAddress, cvAddress, bitNum, value?"1":"0");

	DCC::writeCVBitMain(cvAddress, inDB3, bitNum, value);
}

bool IsAllowedInDCMode(int clientid, unsigned int header, const unsigned int list[], const char *name) {
		int iHeader = 0;
		while (list[iHeader] != 0xFF) {
			if (list[iHeader] == header) {
				return true;
			}
			iHeader++;
		}

		DIAG_Z21(F("[Z21] %d: Forbidden %s 0x%02x in DC mode"), clientid, name, header);
		return false;
}

bool Z21Throttle::parse() {
	bool done = false;
	byte DB[100];
	CircularBuffer* pBuffer = clientsUDP[this->clientid].pudpBuffer;

	if (pBuffer == NULL)
		return false;
	if (pBuffer->isEmpty())
		return false;

	int lengthData = pBuffer->GetInt16() - 4;	// length of the data = total length - length of length (!) - length of header
	unsigned int header = pBuffer->GetInt16();
	byte Xheader = 0;
	byte DB0 = 0;
	int nbLocos = 0;
	if (Z21Throttle::DIAGBASE)
		nbLocos = this->countLocos();

	if (lengthData > 0)	{
		pBuffer->GetBytes(DB, lengthData);
		DIAG_Z21DATA(F("[Z21] %d: <- len:%d  header:0x%02x  : 0x%02x 0x%02x 0x%02x 0x%02x 0x%02x 0x%02x 0x%02x 0x%02x 0x%02x 0x%02x"),
					this->clientid, lengthData + 4, header,
					(lengthData > 0)?DB[0]:0,
					(lengthData > 1)?DB[1]:0,
					(lengthData > 2)?DB[2]:0,
					(lengthData > 3)?DB[3]:0,
					(lengthData > 4)?DB[4]:0,
					(lengthData > 5)?DB[5]:0,
					(lengthData > 6)?DB[6]:0,
					(lengthData > 7)?DB[7]:0,
					(lengthData > 8)?DB[8]:0,
					(lengthData > 9)?DB[9]:0);
	}
	else {
		if (header == 0) {
			DIAG_Z21DATA(F("[Z21] %d: <- len_raw:%d"), this->clientid, lengthData + 4);
			return true;
		}
	}

	if (LaboxModes::mainMode == MainMode::DC) {
		if (!IsAllowedInDCMode(this->clientid, header, DCHeaderLanAllowedCommands, "Header")) 
			return false;
	}

	switch (header)	{
		case HEADER_LAN_XPRESS_NET:
			Xheader = DB[0];
			if (LaboxModes::mainMode == MainMode::DC) {
				if (!IsAllowedInDCMode(this->clientid, Xheader, DCXHeaderAllowedCommands, "X_Header")) 
					return false;
			}

			switch (Xheader) {
				case LAN_X_HEADER_GENERAL:
					DB0 = DB[1];
					switch (DB0) { 
					case LAN_X_DB0_GET_VERSION:
						// Verbose diag because used as a ping to check if the Z21 is alive
						DIAG_Z21VERBOSE(F("[Z21] %d: GET_VERSION"), this->clientid);
						break;
					case LAN_X_DB0_GET_STATUS:
						// Verbose diag because used as a ping to check if the Z21 is alive
						DIAG_Z21VERBOSE(F("[Z21] %d: GET_STATUS  "), this->clientid);
						notifyStatus();
						done = true;
						break;
					case LAN_X_DB0_SET_TRACK_POWER_OFF:
						DIAG_Z21(F("[Z21] %d: POWER_OFF"), this->clientid);
						TrackManager::setMainPower(POWERMODE::OFF);
						done = true;
						break;
					case LAN_X_DB0_SET_TRACK_POWER_ON:
						DIAG_Z21(F("[Z21] %d: POWER_ON"), this->clientid);
						TrackManager::setMainPower(POWERMODE::ON);
						done = true;
						break;
					}
					break;
				case LAN_X_HEADER_SET_STOP:
					DIAG_Z21(F("[Z21] %d: EMERGENCY_STOP"), this->clientid);
					//Emergency Stop  (speed code 1)
					// setThrottle will cause a broadcast so notification will be sent
					LOOPLOCOS() { 
						if (this->cabs[loco] != 0)
							DCC::setThrottle(this->cabs[loco], 1, DCC::getThrottleDirection(this->cabs[loco])); 
					}
					done = true;
					break;
				case LAN_X_HEADER_SET_LOCO:
					DB0 = DB[1];
					if (LaboxModes::mainMode == MainMode::DC) {
						if (!IsAllowedInDCMode(this->clientid, DB0, DCXDB0AllowedCommands, "X_DB0")) 
							return false;
					}
					switch (DB0) {
						case LAN_X_DB0_LOCO_DCC14:
							DIAG_Z21(F("[Z21] %d: LOCO DCC 14 SPEED"), this->clientid);
							setSpeed(14, DB[2], DB[3], DB[4]);
							done = true;
							break;
						case LAN_X_DB0_LOCO_DCC28:
							DIAG_Z21(F("[Z21] %d: LOCO DCC 28 SPEED"), this->clientid);
							setSpeed(28, DB[2], DB[3], DB[4]);
							done = true;
							break;
						case LAN_X_DB0_LOCO_DCC128:
							DIAG_Z21(F("[Z21] %d: LOCO DCC 128 SPEED"), this->clientid);
							setSpeed(128, DB[2], DB[3], DB[4]);
							done = true;
							break;
						case LAN_X_DB0_SET_LOCO_FUNCTION:
							DIAG_Z21(F("[Z21] %d: LOCO DCC FUNCTION"), this->clientid);
							setFunction(DB[2], DB[3], DB[4]);							
							if (Z21Throttle::DIAGBASE) {
								// Debug capacity to print data...
								byte function = DB[4];
								bitClear(function, 6);
								bitClear(function, 7);
								if (function == 12) { // why not ?
									printClientsUDP();
									printThrottles(true);
								}
							}
							done = true;
							break;
					}
					break;
				case LAN_X_HEADER_GET_LOCO_INFO:
					// Verbose diag because used as a ping to check if the Z21 is alive
					DIAG_Z21VERBOSE(F("[Z21] %d: LOCO %d INFO: "), this->clientid, ((DB[2] & 0x3F) << 8) + DB[3]);
					notifyLocoInfo(DB[2], DB[3]);
					done = true;
					break;

				case LAN_X_HEADER_GET_TURNOUT_INFO:
				{
					int id = TURNOUT_FAR_TO_ADDRESS(DB[1], DB[2]);
					DIAG_Z21(F("[Z21] %d: TURNOUT %d INFO"), this->clientid, id);
					if (!Turnout::exists(id)) {
						// If turnout does not exist, create it
						int addr = (id / 4) + 1;
						int subaddr = id % 4;
						DCCTurnout::create(id,addr,subaddr);
						DIAG_Z21(F("[Z21] %d: TURNOUT %d created"), this->clientid, id);
						//Turnout::printAll(&USB_SERIAL);
					}

					notifyTurnoutInfo(DB[1], DB[2]);
					done = true;
				}
					break;

				case LAN_X_HEADER_GET_FIRMWARE_VERSION:
					DIAG_Z21(F("[Z21] %d: FIRMWARE VERSION  "), this->clientid);
					notifyFirmwareVersion();
					done = true;
					break;
				case LAN_X_HEADER_CV_READ:
					if (TrackManager::getProgDriver() != NULL) {
						DIAG_Z21RWCV(F("[Z21] %d: CV READ PROG "), this->clientid);
						// DB0 should be 0x11
						cvReadProg(DB[2], DB[3]);
					}
					else {
						//
						// TODO Dont work today...
						//

						// If no prog track, read on the main track !
						DIAG_Z21RWCV(F("[Z21] %d: CV READ MAIN "), this->clientid);
						// DB0 should be 0x11
						cvReadMain(DB[2], DB[3]);
					}
					done = true;
					break;
				case LAN_X_HEADER_CV_POM:
					DB0 = DB[1];
					switch (DB0) {
						case LAN_X_DB0_CV_POM_WRITE:
						{
							byte code = DB[4] & 0b11111100;
							switch(code)
							{
								case LAN_X_DB3_CV_POM_READ_BYTE:
									// Only by Railcom with Zimo decoders...
									{
										int cvAddress = ((DB[4] & B00000011) << 8) + DB[5] + 1;
										int add = cvReadPom(DB[2], DB[3], DB[4], DB[5]);
										DIAG_Z21RWCV(F("[Z21] %d: CV POM READ BYTE DUMMY cv %d"), this->clientid, cvAddress);
										notifyCvNACK(add);
									}
									break;
								case LAN_X_DB3_CV_POM_WRITE_BYTE:
									DIAG_Z21RWCV(F("[Z21] %d: CV POM WRITE BYTE"), this->clientid);
									cvWriteBytePom(DB[2], DB[3], DB[4], DB[5], DB[6]);
									break;
								case LAN_X_DB3_CV_POM_WRITE_BIT:
									DIAG_Z21RWCV(F("[Z21] %d: CV POM WRITE BIT"), this->clientid);
									cvWriteBitPom(DB[2], DB[3], DB[4], DB[5], DB[6]);
									break;
							}
							done = true;
							break;
						}

						case LAN_X_DB0_CV_POM_ACCESSORY_WRITE:
							DIAG_Z21RWCV(F("[Z21] %d: CV ACCESSORY WRITE POM"), this->clientid);
							break;
					}
					break;
				case LAN_X_HEADER_CV_WRITE:
					DIAG_Z21RWCV(F("[Z21] %d: CV WRITE "), this->clientid);
					cvWriteProg(DB[2], DB[3], DB[4]);
					done = true;
					break;
				case LAN_X_HEADER_SET_TURNOUT:
					setTurnout(DB[1], DB[2], DB[3]);
					done = true;
					break;
      case LAN_X_HEADER_READ_REGISTER:
					break;
			}
			break;

		case HEADER_LAN_SET_BROADCASTFLAGS:
			this->broadcastFlags = CircularBuffer::GetInt32(DB, 0);
			DIAG_Z21BROADCAST(F("[Z21] %d: BROADCAST FLAGS : %s %s %s %s %s %s %s %s %s %s %s"), this->clientid,
							(this->broadcastFlags & BROADCAST_BASE)	? "BASE " : "" ,
							(this->broadcastFlags & BROADCAST_RBUS)	? "RBUS " : "" ,
							(this->broadcastFlags & BROADCAST_RAILCOM)	? "RAILCOM " : "" ,
							(this->broadcastFlags & BROADCAST_SYSTEM)	? "SYSTEM " : "" ,
							(this->broadcastFlags & BROADCAST_BASE_LOCOINFO)	? "LOCOINFO " : "" ,
							(this->broadcastFlags & BROADCAST_LOCONET)	? "LOCONET " : "" ,
							(this->broadcastFlags & BROADCAST_LOCONET_LOCO)	? "LOCONET_LOCO " : "" ,
							(this->broadcastFlags & BROADCAST_LOCONET_SWITCH)	? "LOCONET_SWITCH " : "" ,
							(this->broadcastFlags & BROADCAST_LOCONET_DETECTOR)	? "LOCONET_DETECTOR " : "" ,
							(this->broadcastFlags & BROADCAST_RAILCOM_AUTO)	? "RAILCOM_AUTO " : "" ,
							(this->broadcastFlags & BROADCAST_CAN)	? "CAN" : "" );
			done = true;
			break;
		case HEADER_LAN_GET_LOCOMODE:
			DIAG_Z21VERBOSE(F("[Z21] %d: GET LOCOMODE"), this->clientid);
			notifyLocoMode(DB[0], DB[1]);	// big endian here, but resend the same as received, so no problem.
			done = true;
			break;

		case HEADER_LAN_SET_LOCOMODE:
			DIAG_Z21VERBOSE(F("[Z21] %d: SET LOCOMODE"), this->clientid);
			done = true;
			break;
		case HEADER_LAN_GET_HWINFO:
			DIAG_Z21VERBOSE(F("[Z21] %d: GET HWINFO"), this->clientid);
			notifyHWInfo();	// big endian here, but resend the same as received, so no problem.
			done = true;
			break;
		case HEADER_LAN_LOGOFF:
			DIAG_Z21VERBOSE(F("[Z21] %d: LOGOFF"), this->clientid);
			this->clientid = -1;
			done = true;
			break;
		case HEADER_LAN_SYSTEMSTATE_GETDATA:
			DIAG_Z21VERBOSE(F("[Z21] %d: SYSTEMSTATE GETDATA"), this->clientid);
			notifyStatus();	// big endian here, but resend the same as received, so no problem.
			done = true;
			break;
    case HEADER_LAN_LOCONET_DETECTOR:
    {
      switch(DB0) {
				case LAN_LOCONET_TYPE_UHL_REPORTER:
					{
					uint16_t addr = (DB[2] << 8) + DB[3];
					DIAG_Z21VERBOSE(F("[Z21] %d LOCONET DETECTOR %d"), this->clientid, addr);
					notifySensor(addr);
					//done = true;
					break;
					}
				case LAN_LOCONET_TYPE_DIGITRAX:
				case LAN_LOCONET_TYPE_UHL_LISSY:
					break;
			}
    }
    break;		case HEADER_LAN_GET_SERIAL_NUMBER:
			DIAG_Z21VERBOSE(F("[Z21] %d: GET_SERIAL_NUMBER"), this->clientid);
			notifyFirmwareVersion();
			done = true;
			break;
		case HEADER_LAN_GET_BROADCASTFLAGS:
		case HEADER_LAN_GET_TURNOUTMODE:
		case HEADER_LAN_SET_TURNOUTMODE:
		case HEADER_LAN_RMBUS_DATACHANGED:
		case HEADER_LAN_RMBUS_GETDATA:
		case HEADER_LAN_RMBUS_PROGRAMMODULE:
		case HEADER_LAN_RAILCOM_DATACHANGED:
		case HEADER_LAN_RAILCOM_GETDATA:
		case HEADER_LAN_LOCONET_DISPATCH_ADDR:
			break;
	}

	if (!done) {
    	DIAG_Z21(F("[Z21] %d: not treated :  header:%x   Xheader:%x   DB0:%x"), this->clientid, header, Xheader, DB0);
	}
	else {
		if (Z21Throttle::DIAGBASE) {
			int newNbLocos = this->countLocos();
			if (nbLocos != newNbLocos)
				printLocomotives();
		}
	}
	return true;
}
#endif
