Locoduino/CommandStation-EX-LaBox/DCCACK.cpp

/*
 *  © 2021 M Steve Todd
 *  © 2021 Mike S
 *  © 2021 Fred Decker
 *  © 2020-2025 Harald Barth
 *  © 2020-2022 Chris Harlow
 *  All rights reserved.
 *  
 *  This file is part of CommandStation-EX
 *
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
 *  You should have received a copy of the GNU General Public License
 *  along with CommandStation.  If not, see <https://www.gnu.org/licenses/>.
 */
#include "DCCACK.h"
#include "DIAG.h"
#include "DCC.h"
#include "DCCWaveform.h"
#include "TrackManager.h"

unsigned long DCCACK::minAckPulseDuration = 2000; // micros
unsigned long DCCACK::maxAckPulseDuration = 20000; // micros
  
MotorDriver *  DCCACK::progDriver=NULL;
ackOp  const *  DCCACK::ackManagerProg;
ackOp  const *  DCCACK::ackManagerProgStart;
byte   DCCACK::ackManagerByte;
byte   DCCACK::ackManagerByteVerify;
byte   DCCACK::ackManagerStash;
int    DCCACK::ackManagerWord;
byte   DCCACK::ackManagerRetry;
byte   DCCACK::ackRetry = 2;
int16_t  DCCACK::ackRetrySum;
int16_t  DCCACK::ackRetryPSum;
int    DCCACK::ackManagerCv;
byte   DCCACK::ackManagerBitNum;
bool   DCCACK::ackReceived;
bool   DCCACK::ackManagerRejoin;
volatile uint8_t DCCACK::numAckGaps=0;
volatile uint8_t DCCACK::numAckSamples=0;
uint8_t DCCACK::trailingEdgeCounter=0;


unsigned long DCCACK::ackPulseDuration;  // micros
unsigned long DCCACK::ackPulseStart; // micros
 volatile bool DCCACK::ackDetected;
 unsigned long DCCACK::ackCheckStart; // millis
 volatile bool DCCACK::ackPending;
  bool   DCCACK::autoPowerOff;
   int  DCCACK::ackThreshold; 
   int  DCCACK::ackLimitmA = 50;
     int DCCACK::ackMaxCurrent;
      unsigned int DCCACK::ackCheckDuration; // millis       
    
    
CALLBACK_STATE DCCACK::callbackState=READY;

ACK_CALLBACK DCCACK::ackManagerCallback;

void  DCCACK::Setup(int cv, byte byteValueOrBitnum, ackOp const program[], ACK_CALLBACK callback) {
  // On ESP32 the joined track is hidden from sight (it has type MAIN)
  // and because of that we need first check if track was joined and
  // then unjoin if necessary. This requires that the joined flag is
  // cleared when the prog track is removed.
  ackManagerRejoin=TrackManager::isJoined();
  //DIAG(F("Joined is %d"), ackManagerRejoin);
  if (ackManagerRejoin) {
    // Change from JOIN must zero resets packet.
    TrackManager::setJoin(false);
    DCCWaveform::progTrack.clearResets();
  }
  progDriver=TrackManager::getProgDriver();
  //DIAG(F("Progdriver is %d"), progDriver);
  if (progDriver==NULL) {
    if (ackManagerRejoin) {
      DIAG(F("Joined but no Prog track"));
      TrackManager::setJoin(false);
    }
		DCC::endProgTrackProcessing(-1);
    callback(-3); // we dont have a prog track!
    return;
  }
  if (!progDriver->canMeasureCurrent()) {
    TrackManager::setJoin(ackManagerRejoin);
		DCC::endProgTrackProcessing(-1);
    callback(-2); // our prog track cant measure current
    return;
  }

   autoPowerOff=false;
   if (progDriver->getPower() == POWERMODE::OFF) {
        autoPowerOff=true;  // power off afterwards
        if (Diag::ACK) DIAG(F("Auto Prog power on"));
        progDriver->setPower(POWERMODE::ON);
	
    /* TODO !!! in MotorDriver surely!
    if (MotorDriver::commonFaultPin)
	  DCCWaveform::mainTrack.setPowerMode(POWERMODE::ON);
        DCCWaveform::progTrack.clearResets();
   **/
      }


  ackManagerCv = cv;
  ackManagerProg = program;
  ackManagerProgStart = program;
  ackManagerRetry = ackRetry;
  ackManagerByte = byteValueOrBitnum;
  ackManagerByteVerify = byteValueOrBitnum;
  ackManagerBitNum=byteValueOrBitnum;
  ackManagerCallback = callback;
}

void  DCCACK::Setup(int wordval, ackOp const program[], ACK_CALLBACK callback) {
  ackManagerWord=wordval;
  Setup(0, 0, program, callback);
  }

const byte RESET_MIN=8;  // tuning of reset counter before sending message

// checkRessets return true if the caller should yield back to loop and try later.
bool DCCACK::checkResets(uint8_t numResets) {
  return DCCWaveform::progTrack.getResets() < numResets;
}
// Operations applicable to PROG track ONLY.
// (yes I know I could have subclassed the main track but...) 

void DCCACK::setAckBaseline() {
      int baseline=progDriver->getCurrentRaw();
      ackThreshold= baseline + progDriver->mA2raw(ackLimitmA);
      if (Diag::ACK) DIAG(F("ACK baseline=%d/%dmA Threshold=%d/%dmA Duration between %lus and %lus"),
			  baseline,progDriver->raw2mA(baseline),
			  ackThreshold,progDriver->raw2mA(ackThreshold),
                          minAckPulseDuration, maxAckPulseDuration);
}

void DCCACK::setAckPending() {
      ackMaxCurrent=0;
      ackPulseStart=0;
      ackPulseDuration=0;
      ackDetected=false;
      ackCheckStart=millis();
      numAckSamples=0;
      numAckGaps=0;
      ackPending=true;  // interrupt routines will now take note
}
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
